micovo/200sx-s13-digital-speedo/kicad/DisplayBoard.kicad_sch

## KiCad design kicad/DisplayBoard.kicad_sch (2026-01-31)

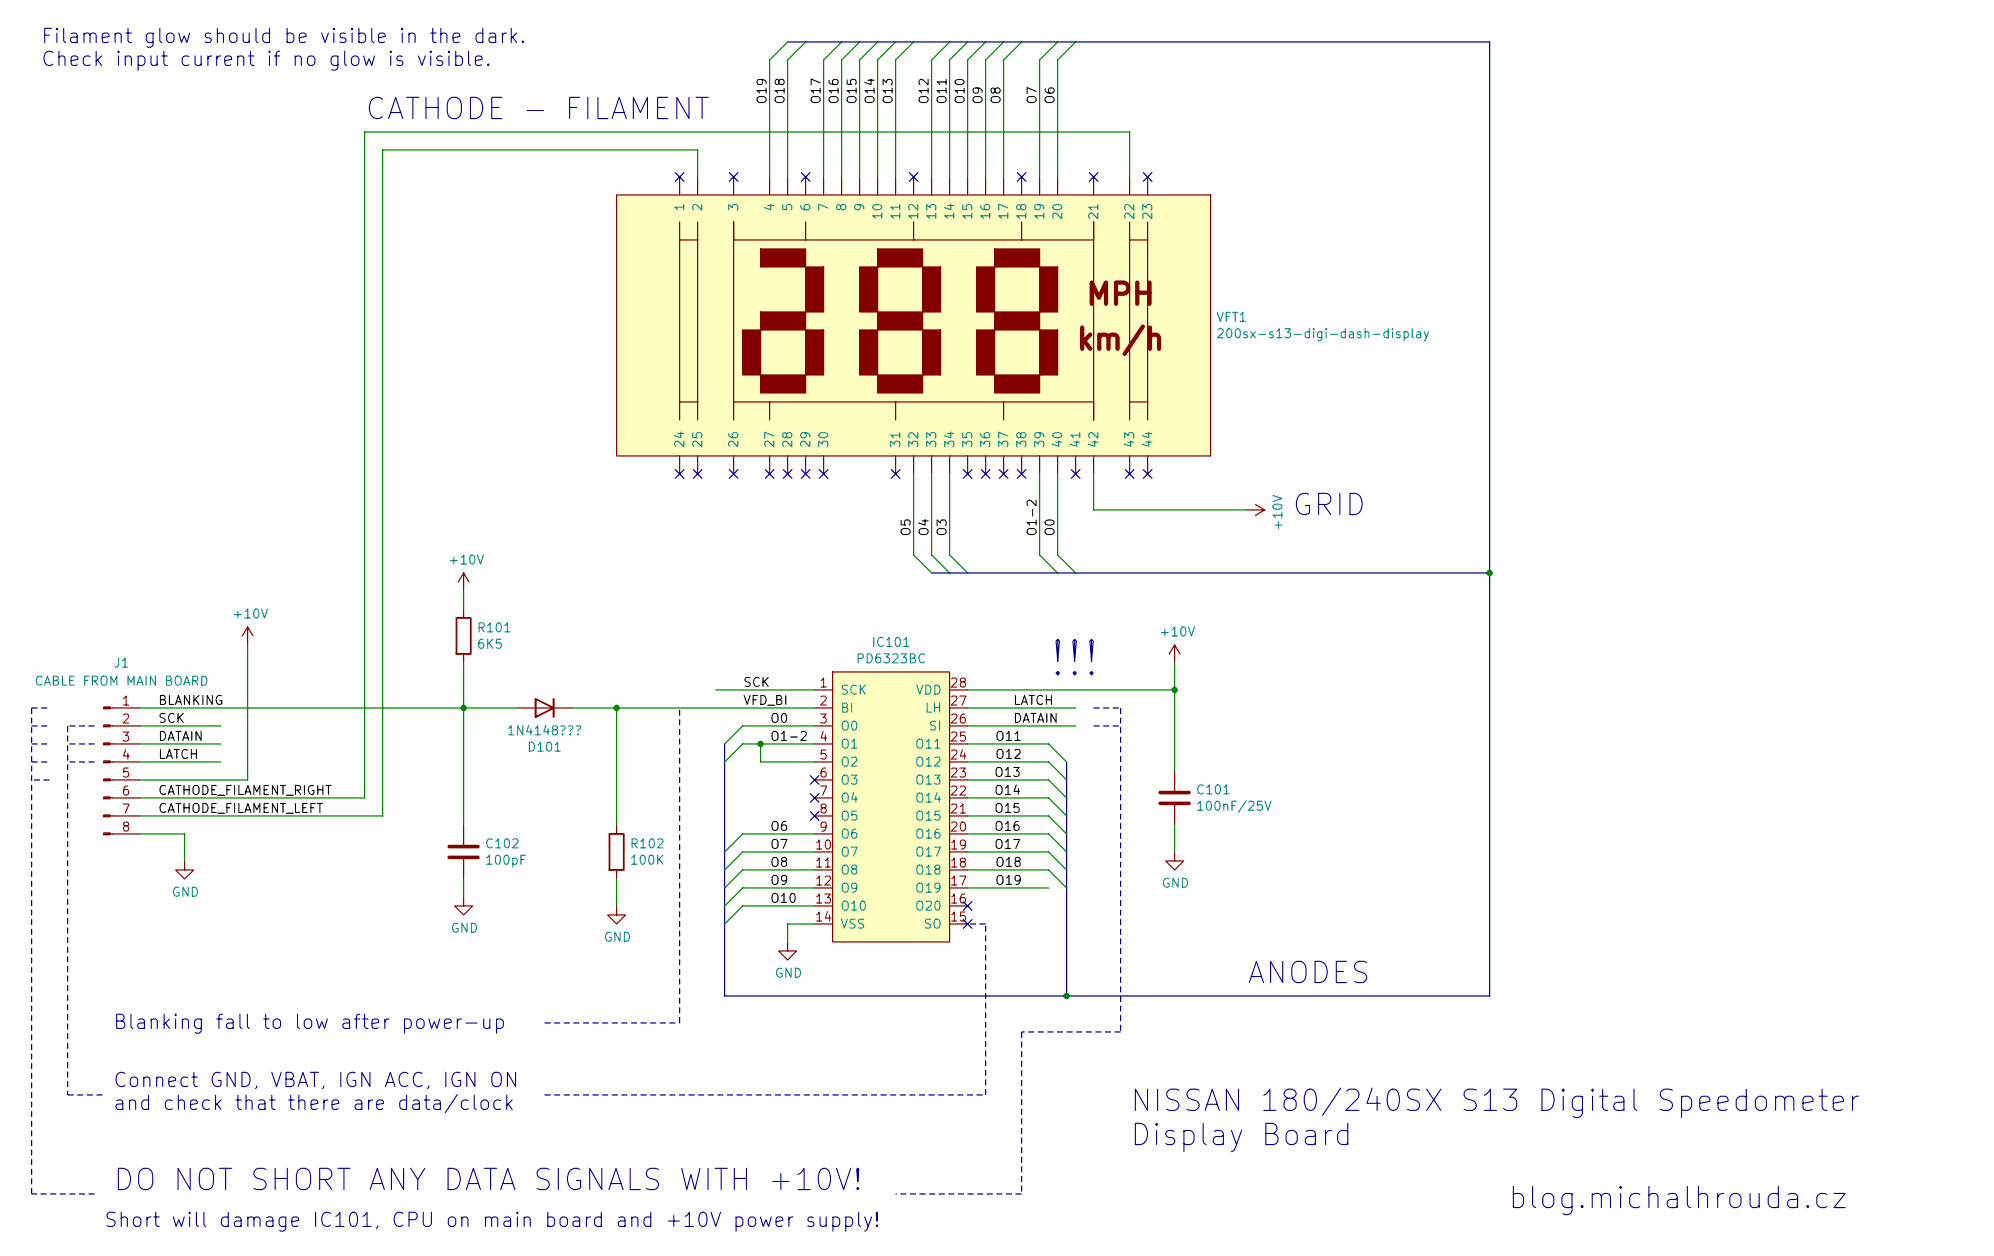
[picture p16: schematic DisplayBoard.kicad_sch]

Parts:
C101: 100nF/25V
C102: 100pF
D101: 1N4148???
IC101: PD6323BC
J1: CABLE FROM MAIN BOARD
R101: 6K5
R102: 100K
VFT1: 200sx-s13-digi-dash-display

Connections:
+10V: C101.1, IC101.28 (VDD), J1.5, R101.1, VFT1.~
BLANKING: C102.1, D101.2 (A), J1.1, R101.2
CATHODE_FILAMENT_LEFT: J1.7, VFT1.~
CATHODE_FILAMENT_RIGHT: J1.6, VFT1.~
DATAIN: IC101.26 (SI), J1.3
GND: C101.2, C102.2, IC101.14 (VSS), J1.8, R102.2
LATCH: IC101.27 (LH), J1.4
O0: IC101.3 (O0), VFT1.~
O1-2: IC101.4 (O1), IC101.5 (O2), VFT1.~
O3: VFT1.~
O4: VFT1.~
O5: VFT1.~
O6: IC101.9 (O6), VFT1.~
O7: IC101.10 (O7), VFT1.~
O8: IC101.11 (O8), VFT1.~
O9: IC101.12 (O9), VFT1.~
O10: IC101.13 (O10), VFT1.~
O11: IC101.25 (O11), VFT1.~
O12: IC101.24 (O12), VFT1.~
O13: IC101.23 (O13), VFT1.~
O14: IC101.22 (O14), VFT1.~
O15: IC101.21 (O15), VFT1.~
O16: IC101.20 (O16), VFT1.~
O17: IC101.19 (O17), VFT1.~
O18: IC101.18 (O18), VFT1.~
O19: IC101.17 (O19), VFT1.~
SCK: IC101.1 (SCK), J1.2
VFD_BI: D101.1 (K), IC101.2 (BI), R102.1

Notes on the sheet:
CATHODE - FILAMENT
!!!
NISSAN 180/240SX S13 Digital Speedometer Display Board
blog.michalhrouda.cz
DO NOT SHORT ANY DATA SIGNALS WITH +10V!
Connect GND, VBAT, IGN ACC, IGN ON and check that there are data/clock
Blanking fall to low after power-up
Short will damage IC101, CPU on main board and +10V power supply!
Filament glow should be visible in the dark. Check input current if no glow is visible.
ANODES
GRID
