micovo/200sx-s13-digital-speedo/kicad/HybridIc2.kicad_sch

## KiCad design kicad/HybridIc2.kicad_sch (2026-01-31)

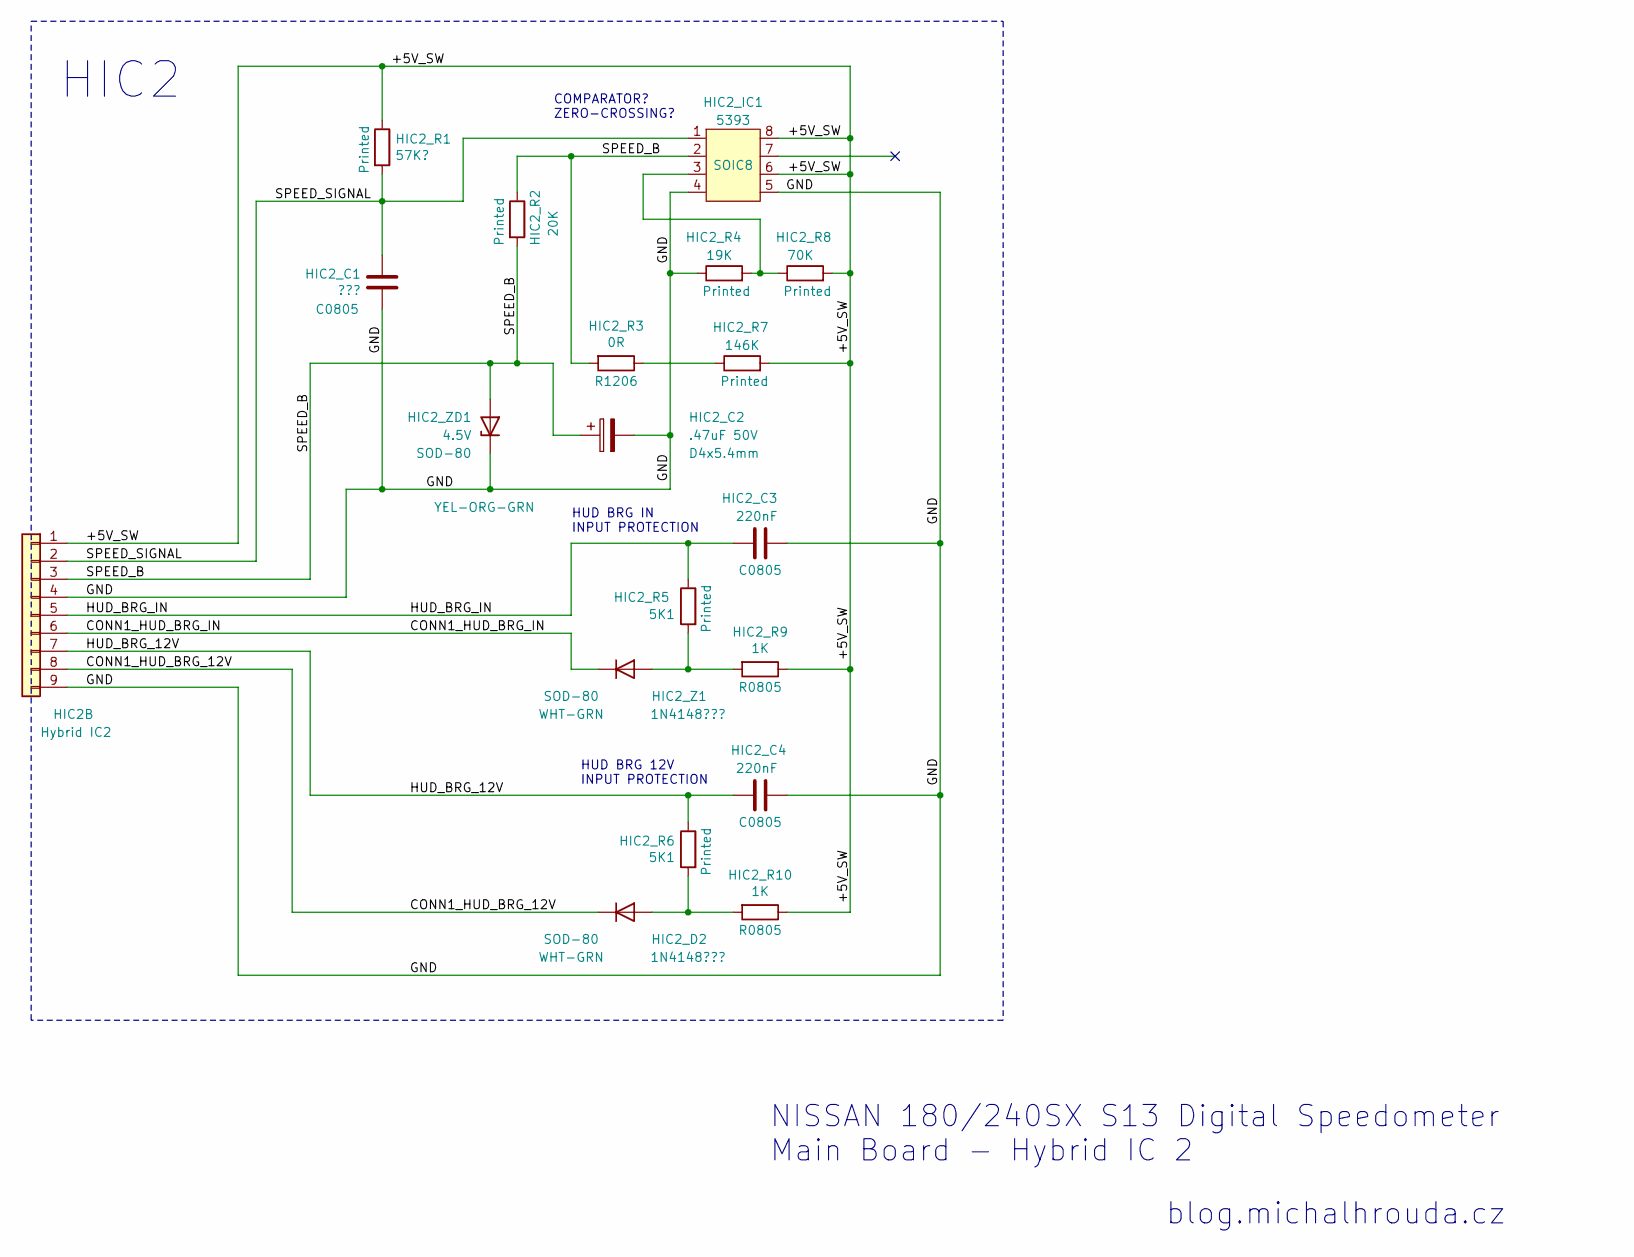
[picture p18: schematic HybridIc2.kicad_sch]

Parts:
HIC2B: Hybrid IC2
HIC2_C1: ???
HIC2_C2: .47uF 50V
HIC2_C3, HIC2_C4: 220nF
HIC2_D2, HIC2_Z1: 1N4148???
HIC2_IC1: 5393
HIC2_R1: 57K?
HIC2_R2: 20K
HIC2_R3: 0R
HIC2_R4: 19K
HIC2_R5, HIC2_R6: 5K1
HIC2_R7: 146K
HIC2_R8: 70K
HIC2_R9, HIC2_R10: 1K
HIC2_ZD1: 4.5V

Connections:
+5V_SW: HIC2B.1, HIC2_IC1.6, HIC2_IC1.8, HIC2_R1.1, HIC2_R7.2, HIC2_R8.2, HIC2_R9.1, HIC2_R10.1
CONN1_HUD_BRG_12V: HIC2B.8, HIC2_D2.1 (K)
CONN1_HUD_BRG_IN: HIC2B.6, HIC2_Z1.1 (K)
GND: HIC2B.4, HIC2B.9, HIC2_C1.2, HIC2_C2.2, HIC2_C3.1, HIC2_C4.1, HIC2_IC1.4, HIC2_IC1.5, HIC2_R4.1, HIC2_ZD1.1 (K)
HUD_BRG_12V: HIC2B.7, HIC2_C4.2, HIC2_R6.1
HUD_BRG_IN: HIC2B.5, HIC2_C3.2, HIC2_R5.1
unnamed: HIC2_D2.2 (A), HIC2_R6.2, HIC2_R10.2
unnamed: HIC2_IC1.3, HIC2_R4.2, HIC2_R8.1
unnamed: HIC2_R3.1, HIC2_R7.1
unnamed: HIC2_R5.2, HIC2_R9.2, HIC2_Z1.2 (A)
SPEED_B: HIC2B.3, HIC2_C2.1, HIC2_IC1.2, HIC2_R2.1, HIC2_R2.2, HIC2_R3.2, HIC2_ZD1.2 (A)
SPEED_SIGNAL: HIC2B.2, HIC2_C1.1, HIC2_IC1.1, HIC2_R1.2

Notes on the sheet:
COMPARATOR? ZERO-CROSSING?
HUD BRG IN INPUT PROTECTION
blog.michalhrouda.cz
HUD BRG 12V INPUT PROTECTION
HIC2
NISSAN 180/240SX S13 Digital Speedometer Main Board - Hybrid IC 2
